mangtronix/Magnesynth/Modules/CB-100 Center Bridge with handle/CB-100 CenterBridge with handle.stl

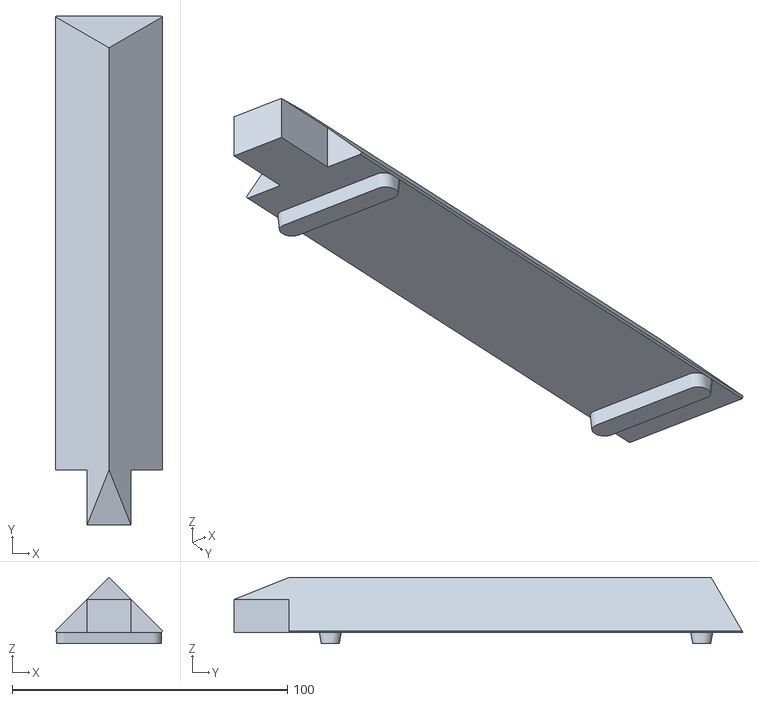
[picture p14: CAD file, 2025-03-18]
Modules/CB-100 Center Bridge with handle/CB-100 CenterBridge with handle.stl
39.0 x 185.0 x 24.0
