mangtronix/Magnesynth/Modules/F-100 Foot/F-100 Foot.stl

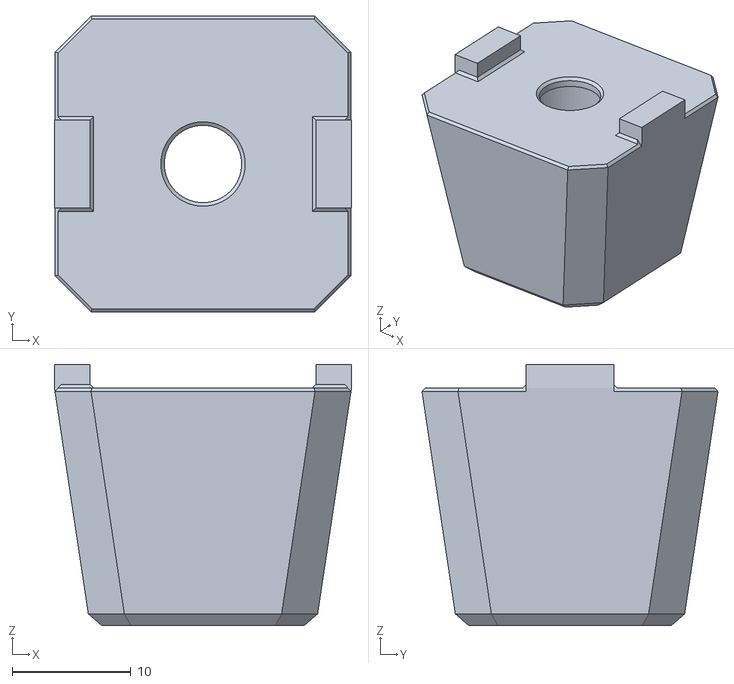
[picture p15: CAD file, 2025-03-18]
Modules/F-100 Foot/F-100 Foot.stl
25.0 x 24.9 x 22.0
