mangtronix/Magnesynth/Modules/TOOL-100 String holder cut guide/TOOL-100 String holder cut guide.stl

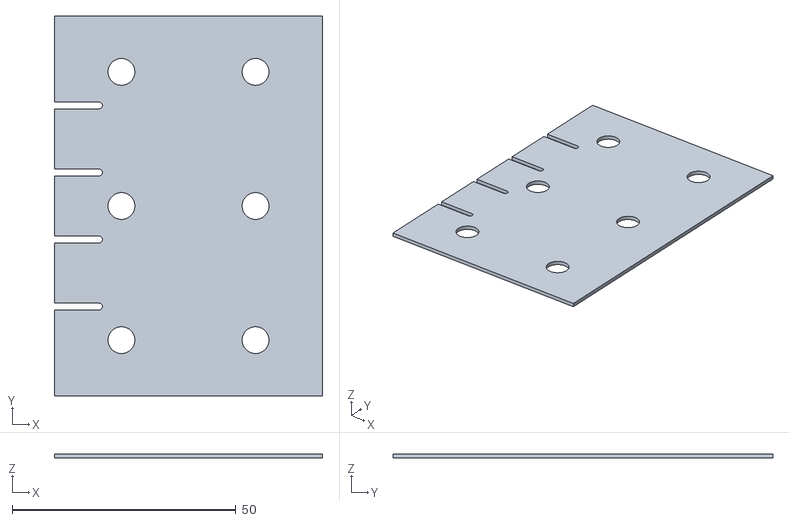
[picture p16: CAD file, 2025-03-18]
Modules/TOOL-100 String holder cut guide/TOOL-100 String holder cut guide.stl
60.0 x 85.0 x 1.00
