mangtronix/Magnesynth/Modules/SH-100 Shelf/SH-100-M Shelf Middle.stl

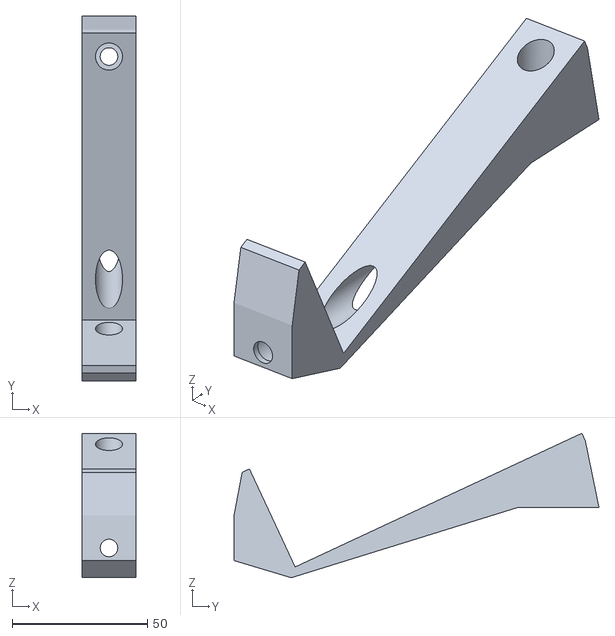
[picture p17: CAD file, 2025-03-18]
Modules/SH-100 Shelf/SH-100-M Shelf Middle.stl
20.0 x 135.0 x 53.4
